snorklerjoe/aprs-weather-station/hardware/ltspice/125Mhz_LP_filter_calculator.asc

C1: cap; 47p
C2: cap; 36p
C3: cap; 13p
C4: cap; 470p
L1: ind; 33n; Rser=0.75
L2: ind; 120n; Rser=0.65
L3: ind; 96n; Rser=0.16
R1: res; {R}
V1: voltage; ""; AC 1; Rser=R2
Named nets: 0
.ac dec 175 50Meg 300Meg
.step param R 10 200 50
.step param R2 10 200 50
