snorklerjoe/aprs-weather-station/hardware/ltspice/AD9850.asc

C1: cap; 22p
C2: cap; 33p
C3: cap; 22p
C4: cap; 22p
C5: cap; 1p
C6: cap; 5.6p
C7: cap; 4.7p
C8: cap; 8p
C9: cap; 3p
D1: diode
D2: diode
D3: diode
D4: diode
I1: current; SINE(-10.24m 10.24m {FREQ} 0 0 0)
I2: current; SINE(-10.24m 10.24m {FREQ} {1/FREQ/2} 0 0)
L1: ind; 470n
L2: ind; 390n
L3: ind; 390n
R1: res; 200
R2: res; 200
R3: res; 1K
R4: res; 500K
R5: res; 100
V2: voltage; 1.5
V4: voltage; 1.5
Named nets: 0, sine_out, comp, reg
