snorklerjoe/aprs-weather-station/hardware/ltspice/Draft2.asc

C1: cap; 12p
C2: cap; 56p
C3: cap; 5.6p
C4: cap; 470p
L1: ind; 12n
R1: res; 5
R2: res; 50
V1: voltage; SINE(0 200m 144.39Meg 0 0 0)
Named nets: 0
.MODEL DI_MMBTH10  NPN (IS=1.26e-016 NF=1.00 BF={beta} VAF=114
+ IKF=24.3m ISE=1.28p NE=2.00 BR=4.00 NR=1.00
+ VAR=16.0 IKR=60.0m RE=1.51 RB=6.05 RC=0.605
+ XTB=1.5 CJE=6.27p VJE=1.10 MJE=0.500 CJC=2.02p VJC=0.300
+ MJC=0.300 TF=130p TR=27.4n EG=1.12 )
.tran 0 2u 0 50p
.meas reQ1 AVG (V(Q1B)-V(Q1E))/Ic(Q1)
