snorklerjoe/aprs-weather-station/hardware/ltspice/mixer.asc

D1: schottky; PMEG2010AEB
D2: schottky; PMEG2010AEB
D3: schottky; PMEG2010AEB
D4: schottky; PMEG2010AEB
L1: ind2; 50n
L2: ind2; 50n
L3: ind2; 50n
L4: ind2; 50n
L5: ind2; 50n
L6: ind2; 50n
L7: ind2; 50n
L8: ind2; 50n
Named nets: RF, LO, IF, 0
K1 L1 L2 L3 L4 0.95
K2 L5 L6 L7 L8 0.95
