snorklerjoe/aprs-weather-station/hardware/ltspice/Ring_Diode_Mixer.asc

D5: diode
D6: diode
D7: diode
D8: diode
L1: ind2; 20µ
L2: ind2; 23µ
L3: ind2; 20µ
L4: ind2; 20µ
L5: ind2; 23µ
L6: ind2; 20µ
Named nets: IN+, LO+, OUT, LO-, 0, IN-
K1 L1 L2 L3 1
K2 L4 L5 L6 1
