snorklerjoe/aprs-weather-station/hardware/ltspice/update_03012022.asc

C1: cap; 22p
C2: cap; 33p
C3: cap; 22p
C4: cap; 22p
C5: cap; 1p
C6: cap; 5.6p
C7: cap; 4.7p
C8: cap; 13p; Rser={C_RES}
C9: cap; 470p; Rser={C_RES}
C10: cap; 2000p
C11: cap; 470p
C12: cap; 1500p
C13: cap; 2000p
C14: cap; 0.022µ
C15: cap; 470p; Rser=.1
C16: cap; 3.3p; Rser=.1
C17: cap; 1n
C18: cap; 150p; Rser=.1
C23: cap; 470p
C24: cap; 470p; Rser={C_RES}
C25: cap; 100p
C28: cap; 2000p
C31: cap; 36p; Rser={C_RES}
C32: cap; 47p; Rser={C_RES}
C42: cap; 0.022µ
C43: cap; 470p
C47: cap; 470p
C71: cap; 150p; Rser=.1
C72: cap; 240p; Rser=.1
C73: cap; 3.85p; Rser=.1
C74: cap; 3.85p; Rser=.1
L1: ind; 470n
L2: ind; 390n
L3: ind2; 390n
L4: ind2; 96n
L5: ind; 150n; Rser=.1
L6: ind; 120n
L7: ind; 7.5n; Rser=.1
L8: ind; 120n
L9: ind; 130n
L15: ind; 0.1n
L17: ind; 4.7µ
L18: ind; 33n
L19: ind; 120n
L21: ind; 270n
L22: ind; 270n
L23: ind2; 160n
L24: ind2; 71.3n
L38: ind; 7.5n; Rser=.1
L39: ind; 4.7n; Rser=.1
L40: ind; 270n; Rser=.1
L41: ind; 270n; Rser=1
Q1: npn; DI_MMBTH10
Q4: npn; DI_MMBTH10
Q9: npn; DI_MMBTH10
R1: res; 680
R2: res; 47
R3: res; 0
R4: res; 0.8k
R5: res; 1.2k
R6: res; 40
R7: res; 50
R8: res; 75k
R9: res; 50k
R10: res; 50
R12: res; 0
R15: res; 1.2k
R17: res; 1.8k
R18: res; 150
R21: res; 75
R22: res; 100
R39: res; 30
R42: res; 470
R43: res; 68
R44: res; 510
U1: AD9850; FREQ=19.39Meg
V1: voltage; SINE(0 200m 125Meg); Rser=50
V2: voltage; ""; AC 1
V5: voltage; PULSE(0.3 3.1 0 325p 225p {1/125Meg/2} {1/125Meg})
V6: voltage; 5
X1: mixer
Named nets: 0, Q1B, Q1E, test
.tran 0 5u 2.5u 0.0000000001
LP filter
.model idealDiode D(Ron=0 Roff=100Meg Vfwd=0)
.param c_res=0.01
LP filter
.model my2N2222 NPN(IS=1E-14 VAF=100 BF={beta} IKF=0.3 XTB=1.5 BR=3 CJC=8E-12 CJE=25E-12 TR=100E-9 TF=400E-12 ITF=1 VTF=2 XTF=3 RB=10 RC=.3 RE=.2 Vceo=30 Icrating=800m mfg=NXP)
.step param beta 120 300 175
.MODEL DI_MMBTH10  NPN (IS=1.26e-016 NF=1.00 BF={beta} VAF=114
+ IKF=24.3m ISE=1.28p NE=2.00 BR=4.00 NR=1.00
+ VAR=16.0 IKR=60.0m RE=1.51 RB=6.05 RC=0.605
+ XTB=1.5 CJE=6.27p VJE=1.10 MJE=0.500 CJC=2.02p VJC=0.300
+ MJC=0.300 TF=130p TR=27.4n EG=1.12 )
6:4
K1 L23 L24 0.95
.meas reQ9 AVG (V(Q1B)-V(Q1E))/Ic(Q9)
.meas reQ11 AVG (V(Q11B)-V(Q11E))/Ic(Q11)
.param beta=200
.meas reQ12 AVG (V(Q12B)-V(Q12E))/Ic(Q12)
* Q2SCR562F3 NPN BJT model
* PKG: HUML2020L3,Vceo=30V,Ic=6A
* Model Generated by ROHM
* All Rights Reserved
* Commercial Use or
* Resale Restricted
* Date: 2016/05/09
.MODEL Q2SCR562F3 NPN
+ IS=2.7000E-12
+ BF=359.65
+ VAF=47.246
+ IKF=17.794
+ ISE=5.1063E-12
+ NE=1.6800
+ BR=164.76
+ VAR=13.821
+ IKR=10.533
+ ISC=5.5359E-12
+ NC=2.3044
+ NK=.54944
+ RE=2.0000E-3
+ RB=2.3516
+ RC=35.434E-3
+ CJE=711.58E-12
+ VJE=.77165
+ MJE=.37592
+ CJC=152.75E-12
+ VJC=.55108
+ MJC=.39358
+ TF=359.46E-12
+ XTF=415.35
+ VTF=248.34
+ ITF=34.139
+ TR=7.0435E-9
+ XTB=1.5000
+ TRE1=0.05
was 2k
was 0.1nH
was 0.1nH
was 75
was 30k
was 30
changed
https://miguelvaca.github.io/vk3cpu/toroid.html
